Nomisimo/MiniHead/Firmware/MiniHead/main/plugins/artnet/artnet_panel_html.h

#pragma once

// ── Art-Net Patch Panel HTML Fragment ────────────────────────────
// Served at GET /plugins/artnet/panel.html
// Injected into #artnet-module-container by the main page JS.
// All JS globals are prefixed an_ and wrapped in an IIFE.
// Matches PC App artnet_panel.html exactly.
// ─────────────────────────────────────────────────────────────────

const char ARTNET_PANEL_HTML[] PROGMEM = R"=====(
<style>
  .an-title{font-family:var(--mono);font-size:11px;color:var(--accent);letter-spacing:3px;text-transform:uppercase;margin-bottom:14px;padding-bottom:10px;border-bottom:1px solid var(--border);}
  .an-row{display:flex;align-items:center;gap:8px;flex-wrap:wrap;margin-bottom:10px;}
  .an-label{font-family:var(--mono);font-size:11px;color:var(--text-dim);white-space:nowrap;}
  .an-num{width:52px;background:var(--surface2);border:1px solid var(--border);color:var(--text);padding:4px 6px;font-family:var(--mono);font-size:12px;border-radius:3px;text-align:center;-moz-appearance:textfield;}
  .an-num::-webkit-outer-spin-button,.an-num::-webkit-inner-spin-button{-webkit-appearance:none;}
  .an-uni-nav{display:flex;align-items:center;gap:6px;margin-bottom:8px;}
  #an_grid{display:grid;grid-template-columns:repeat(32,minmax(18px,1fr));gap:1px;background:var(--border);border:1px solid var(--border);border-radius:4px;overflow:hidden;margin-bottom:4px;cursor:crosshair;}
  .an-cell{aspect-ratio:1;min-width:18px;background:var(--surface2);display:flex;align-items:center;justify-content:center;overflow:hidden;transition:filter 0.08s;font-size:9px;color:rgba(0,0,0,0.8);font-family:var(--mono);font-weight:700;line-height:1;user-select:none;}
  .an-cell:hover{filter:brightness(1.5);}
  .net-btn{padding:5px 12px;border:1px solid var(--border);background:var(--surface2);color:var(--text);font-family:var(--mono);font-size:11px;cursor:pointer;border-radius:3px;touch-action:manipulation;transition:border-color 0.1s,color 0.1s,opacity 0.1s;}
  .net-btn:hover{border-color:var(--text-dim);}
  .net-btn:active{opacity:0.65;}
  .net-btn.primary{border-color:var(--accent);color:var(--accent);}
  .net-btn.sm{padding:3px 8px;font-size:10px;}
</style>

<div class="an-title">// Art-Net Patch</div>

<!-- Bulk patch row -->
<div class="an-row">
  <span class="an-label">Bulk:</span>
  <span class="an-label">Uni</span>
  <input type="number" id="an_bulkUni" class="an-num" value="1" min="1" max="32767">
  <span class="an-label">.</span>
  <span class="an-label">Addr</span>
  <input type="number" id="an_bulkAddr" class="an-num" value="1" min="1" max="512">
  <span class="an-label">&times;</span>
  <input type="number" id="an_bulkCount" class="an-num" value="1" min="1" max="32" style="width:40px;">
  <span class="an-label">lamps&nbsp;&nbsp;Fix#</span>
  <input type="number" id="an_bulkFix" class="an-num" value="1" min="1" max="999" style="width:48px;">
  <button class="net-btn primary" onclick="an_bulk()">PATCH</button>
</div>
<!-- Action row -->
<div class="an-row" style="margin-bottom:4px;">
  <button class="net-btn primary" onclick="an_patchSelected()">PATCH SELECTED</button>
  <span style="flex:1;"></span>
  <button class="net-btn" onclick="an_clearUniverse()">CLEAR UNIVERSE</button>
  <button class="net-btn" style="color:var(--danger);border-color:var(--danger);" onclick="an_clearAll()">CLEAR ALL</button>
</div>

<!-- Universe navigation -->
<div class="an-uni-nav">
  <span class="an-label">Universe</span>
  <input type="number" id="an_uniInput" class="an-num" value="0" min="0" max="32767"
    onchange="an_gotoUniverse(parseInt(this.value)||0)">
  <button class="net-btn sm" onclick="an_prevUniverse()">&#9664;</button>
  <button class="net-btn sm" onclick="an_nextUniverse()">&#9654;</button>
  <span class="an-label" id="an_uniInfo" style="margin-left:auto;"></span>
</div>

<!-- 512-slot grid — select one head in Network Heads, then click a cell to patch -->
<div id="an_grid"></div>

<script>
(function(){
  var DMX_FP = 7;
  var an_patches = [], an_fixtures = [];
  var an_curUni = 0;
  // Own patch colour — single fixture per ESP, no fixID in patch any more.
  var OWN_PATCH_COLOR     = 'hsl(200,68%,52%)';
  var OWN_PATCH_COLOR_DIM = 'hsla(200,68%,38%,0.35)';

  function an_load(){
    Promise.all([
      fetch('/api/artnet/patch').then(function(r){return r.json();}),
      fetch('/api/fixtures').then(function(r){return r.json();}).catch(function(){return[];})
    ]).then(function(res){
      an_patches=res[0]; an_fixtures=res[1];
      an_renderGrid();
    }).catch(function(){});
  }

  function an_gotoUniverse(uni){
    an_curUni = Math.max(0, Math.min(32767, uni));
    document.getElementById('an_uniInput').value = an_curUni;
    an_renderGrid();
  }
  function an_prevUniverse(){ an_gotoUniverse(an_curUni - 1); }
  function an_nextUniverse(){ an_gotoUniverse(an_curUni + 1); }

  function an_renderGrid(){
    var grid = document.getElementById('an_grid');
    grid.innerHTML = '';
    var slotMap = {};
    an_patches.forEach(function(p){
      if(p.universe !== an_curUni) return;
      for(var ch=0; ch<DMX_FP; ch++) slotMap[p.startAddr+ch] = p;
    });
    var count = an_patches.filter(function(p){return p.universe===an_curUni;}).length;
    document.getElementById('an_uniInfo').textContent = count ? count+' fixture(s)' : '';

    for(var i=1; i<=512; i++){
      var cell = document.createElement('div');
      cell.className = 'an-cell';
      cell.dataset.addr = i;
      var p = slotMap[i];
      if(p){
        if(i === p.startAddr){
          cell.style.background = OWN_PATCH_COLOR;
          cell.innerHTML = '<div style="display:flex;flex-direction:column;align-items:center;line-height:1.2;">'
            + '<span style="font-size:9px;font-weight:700;color:rgba(0,0,0,0.85);">OWN</span>'
            + '<span style="font-size:7px;font-weight:400;color:rgba(0,0,0,0.5);">'+i+'</span>'
            + '</div>';
          cell.title = 'Own patch \u2014 Addr '+i;
        } else {
          var relCh = i - p.startAddr + 1;
          cell.style.background = OWN_PATCH_COLOR_DIM;
          cell.innerHTML = '<span style="font-size:11px;color:rgba(255,255,255,0.7);">'+relCh+'</span>';
          cell.title = 'Own patch \u2014 Addr '+i+' (ch '+relCh+')';
        }
      } else {
        cell.innerHTML = '<span style="font-size:9px;opacity:0.25;color:#fff;">'+i+'</span>';
        cell.title = 'Addr '+i+' (free)';
      }
      cell.addEventListener('click', function(){
        an_cellClick(parseInt(this.dataset.addr));
      });
      grid.appendChild(cell);
    }
  }

  // Click a grid cell: patches the single selected head (from Network Heads) to that address
  function an_cellClick(addr){
    var ids = (typeof nh_getSelectedFixIDs==='function') ? nh_getSelectedFixIDs() : [];
    if(ids.length !== 1){
      if(typeof toast==='function') toast(ids.length===0 ? 'Select a head in Network Heads first' : 'Select exactly one head to patch','err');
      return;
    }
    if(addr + DMX_FP - 1 > 512){
      if(typeof toast==='function') toast('Not enough room \u2014 use next universe','err');
      return;
    }
    var selFix = ids[0];
    fetch('/api/artnet/patch',{method:'POST',headers:{'Content-Type':'application/json'},
      body:JSON.stringify({fixID:selFix,universe:an_curUni,startAddr:addr})
    }).then(function(r){return r.json();}).then(function(d){
      if(d.status==='ok'){
        if(typeof toast==='function') toast('Patched Fix#'+selFix+' \u2192 Uni '+an_curUni+' Addr '+addr);
        an_load();
      } else if(typeof toast==='function') toast(d.message||'Error','err');
    });
  }

  window.an_updatePatch=function(uni, addr){
    var p=an_patches[0];
    if(!p) return;
    var data={universe:uni!==null?uni:p.universe, startAddr:addr!==null?addr:p.startAddr};
    fetch('/api/artnet/patch/own',{method:'PUT',headers:{'Content-Type':'application/json'},
      body:JSON.stringify(data)
    }).then(function(r){return r.json();}).then(function(d){
      if(d.status==='ok'){
        if(uni!==null) p.universe=uni;
        if(addr!==null) p.startAddr=addr;
        an_renderGrid();
        if(typeof toast==='function') toast('Patch updated');
      }
    });
  };

  window.an_del=function(e){
    if(e) e.stopPropagation();
    fetch('/api/artnet/patch/own',{method:'DELETE'}).then(function(){
      if(typeof toast==='function') toast('Patch removed');
      an_load();
    });
  };

  window.an_bulk=function(){
    var uni   = parseInt(document.getElementById('an_bulkUni').value)   || 1;
    var addr  = parseInt(document.getElementById('an_bulkAddr').value)  || 1;
    var count = parseInt(document.getElementById('an_bulkCount').value) || 1;
    var fix   = parseInt(document.getElementById('an_bulkFix').value)   || 1;
    fetch('/api/artnet/patch/bulk',{method:'POST',headers:{'Content-Type':'application/json'},
      body:JSON.stringify({universe:uni,startAddr:addr,count:count,firstFixID:fix})
    }).then(function(r){return r.json();}).then(function(d){
      if(d.status==='ok'){
        if(typeof toast==='function') toast('Patched '+d.count+' fixture(s)');
        an_gotoUniverse(uni);
        an_load();
      } else if(typeof toast==='function') toast(d.message||'Error','err');
    });
  };

  // ── Patch Selected ───────────────────────────────────────────────
  window.an_patchSelected = function(){
    var ids = (typeof nh_getSelectedFixIDs==='function') ? nh_getSelectedFixIDs() : [];
    if(!ids.length){ if(typeof toast==='function') toast('No heads selected in Network panel','err'); return; }
    var uni  = parseInt(document.getElementById('an_bulkUni').value)  || 1;
    var addr = parseInt(document.getElementById('an_bulkAddr').value) || 1;
    var skipped = 0;
    var toPost = [];
    ids.forEach(function(fixID, i){
      var a = addr + i * DMX_FP;
      if(a + DMX_FP - 1 > 512){ skipped++; return; }
      toPost.push({fixID:fixID, universe:uni, startAddr:a});
    });
    if(!toPost.length){ if(typeof toast==='function') toast('No room in universe '+uni+' \u2014 increase Addr or use next universe','err'); return; }
    var pending = toPost.length;
    toPost.forEach(function(p){
      fetch('/api/artnet/patch',{method:'POST',headers:{'Content-Type':'application/json'},
        body:JSON.stringify(p)
      }).then(function(r){return r.json();}).then(function(){
        if(--pending===0){
          if(typeof toast==='function') toast('Patched '+toPost.length+' fixture(s)'+(skipped?' ('+skipped+' skipped \u2014 overflow)':''));
          an_gotoUniverse(uni);
          an_load();
        }
      });
    });
  };

  // ── Clear Universe ───────────────────────────────────────────────
  window.an_clearUniverse = function(){
    fetch('/api/artnet/patch/universe/'+an_curUni,{method:'DELETE'})
      .then(function(r){return r.json();}).then(function(d){
        if(typeof toast==='function') toast('Universe '+an_curUni+' cleared ('+(d.removed||0)+' patch(es))');
        an_load();
      });
  };

  // ── Clear All ────────────────────────────────────────────────────
  window.an_clearAll = function(){
    if(!an_patches.length){ if(typeof toast==='function') toast('Nothing to clear'); return; }
    fetch('/api/artnet/patch',{method:'DELETE'})
      .then(function(r){return r.json();}).then(function(d){
        if(typeof toast==='function') toast('All patches cleared ('+(d.removed||0)+')');
        an_load();
      });
  };

  window.an_prevUniverse = an_prevUniverse;
  window.an_nextUniverse = an_nextUniverse;
  window.an_gotoUniverse = an_gotoUniverse;

  an_load();
  setInterval(an_load, 5000);
})();
</script>
)=====";
